WHJWNAVY/MiniClock/doc/MiniClock_PCB_Rev190417B/PCB_MINICLOCK-PCB-02_20190419231738/e6bf4326-680b-4851-8b6b-353d8bd95d85.pdf

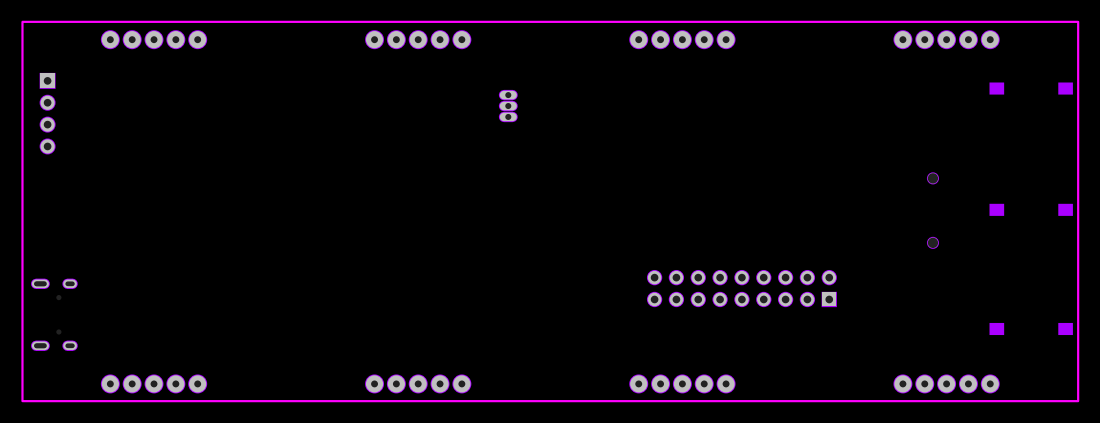
[picture p14: page 1]
