WHJWNAVY/MiniClock/media/IMG_20190427_180634_1_compressed.jpg

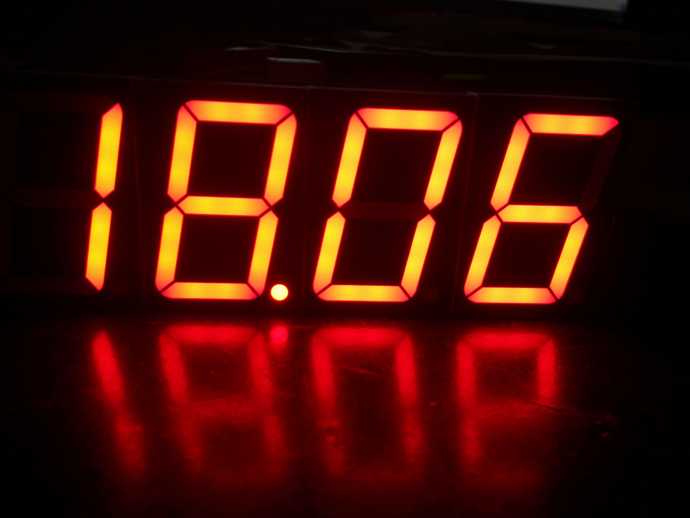
media/IMG_20190427_180634_1_compressed.jpg
