WHJWNAVY/MiniClock/media/IMG_20190427_180716_1_compressed.jpg

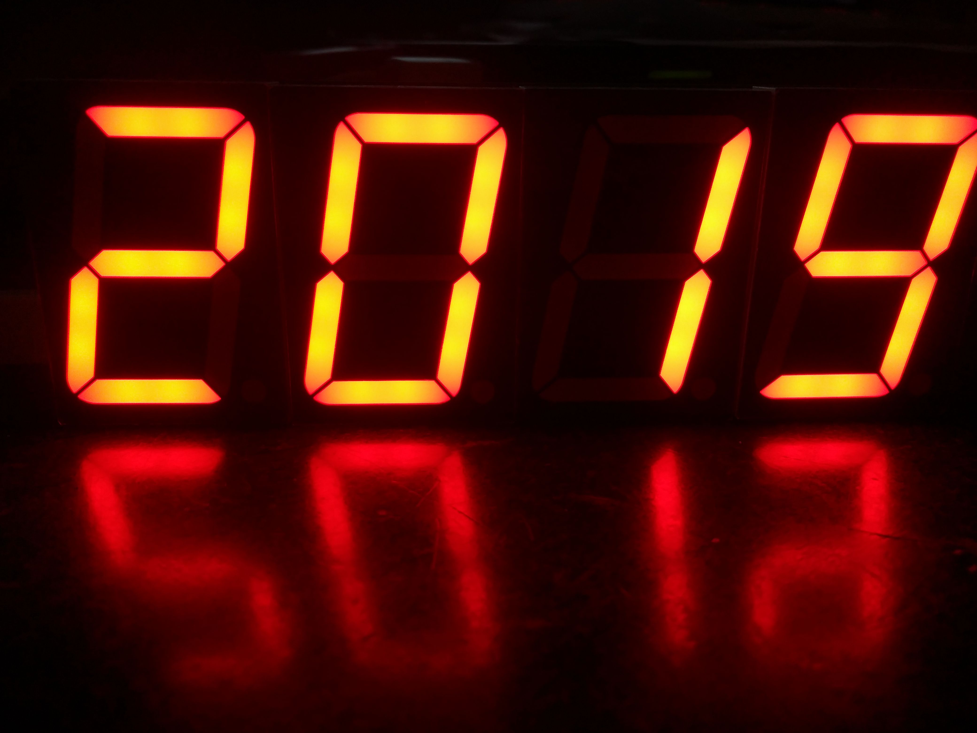
media/IMG_20190427_180716_1_compressed.jpg
