WHJWNAVY/MiniClock/media/IMG_20190427_180908_compressed.jpg

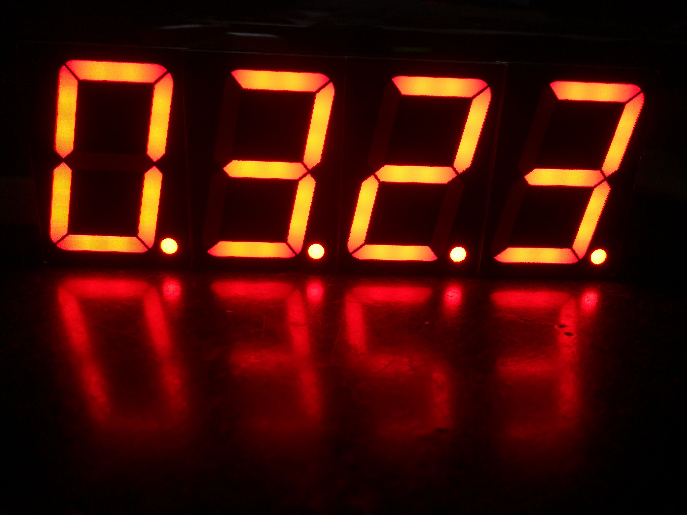
media/IMG_20190427_180908_compressed.jpg
