WHJWNAVY/MiniClock/media/MiniClock0.png

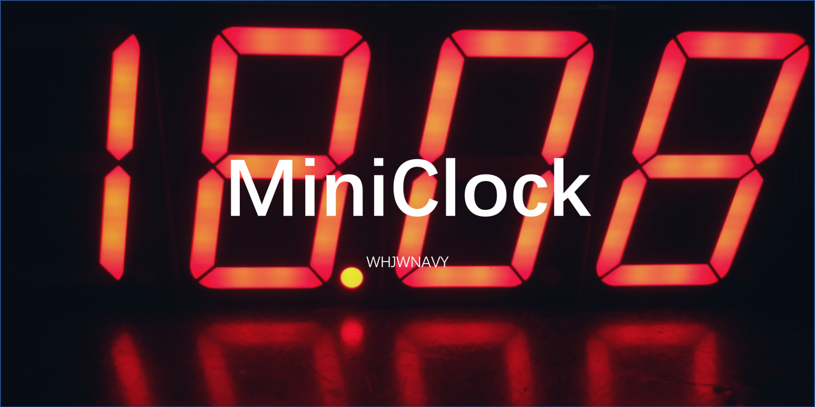
media/MiniClock0.png
