WHJWNAVY/MiniClock/doc/MiniClock_PCB_Rev190417B/PCB_MINICLOCK-PCB-02_20190419231738/f90c94eb-5b3c-4272-8975-5b49941675d2.pdf

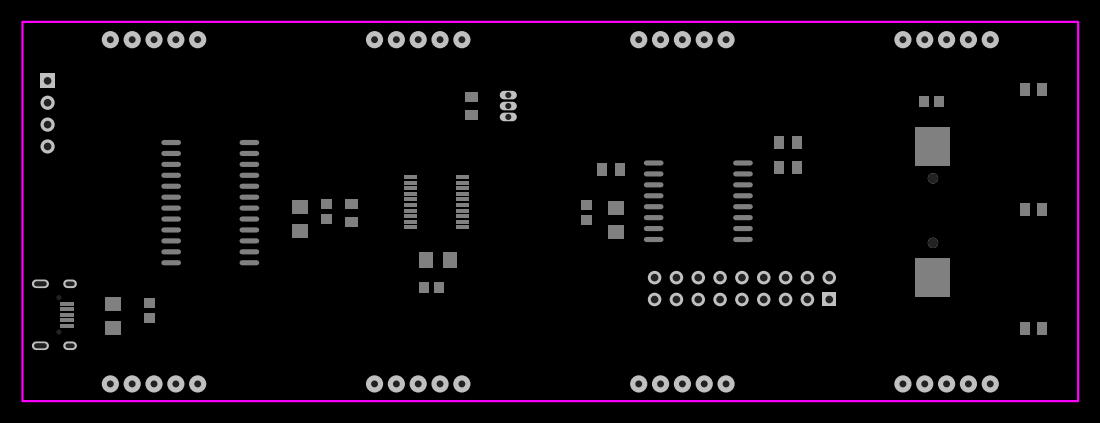
[picture p33: page 1]
