WHJWNAVY/MiniClock/src/drv_1302.h

#ifndef __DRV_1302_H__
#define __DRV_1302_H__

#include "common.h"

extern void rtc_init(void);

/*****************************************************************************
 函 数 名  : rtc_set_time
 功能描述  : 设置当前时间
 输入参数  : time   要设置的时间
 输出参数  : 无
 返 回 值  : 无
*****************************************************************************/
extern void rtc_set_time(rtc_time_t *time);

/*****************************************************************************
 函 数 名  : rtc_read_time
 功能描述  : 获取当前时间
 输入参数  : void
 输出参数  : time   读取到的闹钟时间
 返 回 值  : 无
*****************************************************************************/
extern void rtc_read_time(rtc_time_t *time);

/*****************************************************************************
 函 数 名  : alarm_set_time
 功能描述  : 设置闹钟时间
 输入参数  : time   要设置的闹钟时间
 输出参数  : 无
 返 回 值  : 无
*****************************************************************************/
extern void alarm_set_time(rtc_time_t *time);

/*****************************************************************************
 函 数 名  : alarm_read_time
 功能描述  : 获取闹钟时间
 输入参数  : 无
 输出参数  : time   要设置的闹钟时间
 返 回 值  : 无
*****************************************************************************/
extern void alarm_read_time(rtc_time_t *time);

/*****************************************************************************
 函 数 名  : alarm_set_flag
 功能描述  : 设置闹钟开关
 输入参数  : b      闹钟开启标志
 输出参数  : 无
 返 回 值  : 无
*****************************************************************************/
extern void alarm_set_flag(uchar b);

/*****************************************************************************
 函 数 名  : alarm_get_flag
 功能描述  : 获取闹钟开关
 输入参数  : 无
 输出参数  : 无
 返 回 值  : 闹钟开启标志
*****************************************************************************/
extern uchar alarm_get_flag(void);

/*****************************************************************************
 函 数 名  : alarm_beep
 功能描述  : 控制闹钟响铃
 输入参数  : b      闹钟开始响铃
 输出参数  : 无
 返 回 值  : 无
*****************************************************************************/
extern void alarm_init(rtc_time_t *alarm);

#endif
